naouarouss2/Glowy/CAD/Source Files/PSU.SLDPRT

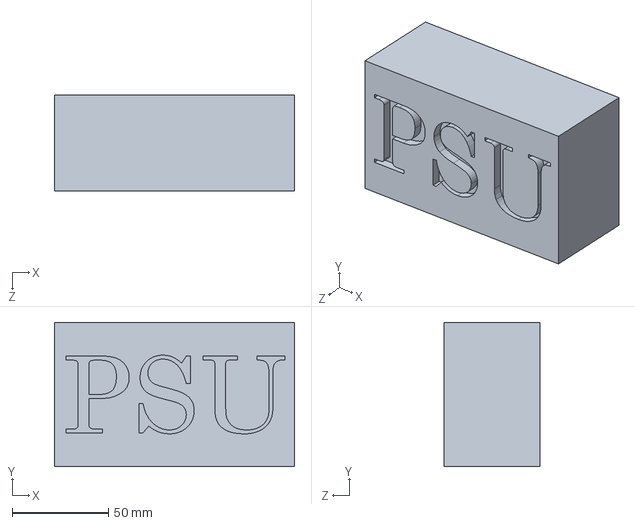
[picture p13: CAD file, 2026-04-14]
CAD/Source Files/PSU.SLDPRT
125.0 x 75.0 x 50.0 mm
