naouarouss2/Glowy/CAD/Laser-Cut Parts/STEP/Bottom.STEP

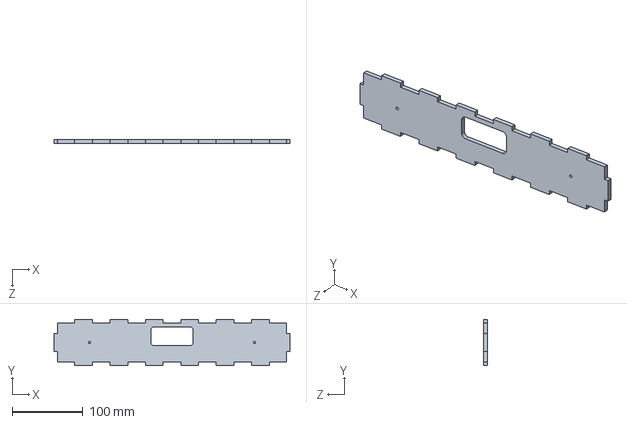
[picture p14: CAD file, 2026-04-09]
CAD/Laser-Cut Parts/STEP/Bottom.STEP
333.3 x 65.2 x 5.00 mm
