naouarouss2/Glowy/CAD/Source Files/MIC.SLDPRT

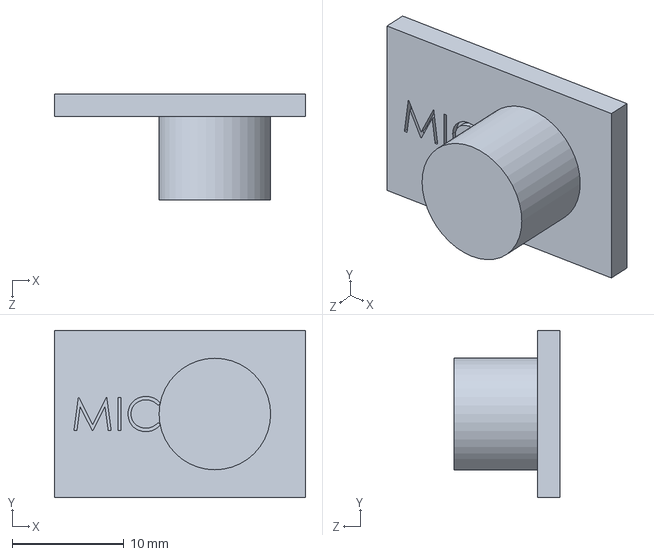
[picture p15: CAD file, 2026-04-14]
CAD/Source Files/MIC.SLDPRT
22.5 x 15.0 x 9.50 mm
